hasenbanck/exa_tim/firmware/Src/power.c

#include "power.h"
#include "clock.h"
#include "config.h"
#include "main.h"
#include "stm32l0xx_hal.h"

extern LPTIM_HandleTypeDef hlptim1;
extern UART_HandleTypeDef hlpuart1;
extern RTC_HandleTypeDef hrtc;
extern SPI_HandleTypeDef hspi1;
extern TIM_HandleTypeDef htim2;

void HAL_TIM_MspPostInit(TIM_HandleTypeDef *htim);

void systemClockConfig(void) {
  RCC_OscInitTypeDef RCC_OscInitStruct;
  RCC_ClkInitTypeDef RCC_ClkInitStruct;
  RCC_PeriphCLKInitTypeDef PeriphClkInit;

  /* Configure the main internal regulator output voltage */
  __HAL_PWR_VOLTAGESCALING_CONFIG(PWR_REGULATOR_VOLTAGE_SCALE2);

  /*  Enable access to backup domain */
  HAL_PWR_EnableBkUpAccess();

  /* Configure LSE Drive Capability */
  __HAL_RCC_LSEDRIVE_CONFIG(RCC_LSEDRIVE_LOW);

  /* Initializes the CPU, AHB and APB busses clocks */
  RCC_OscInitStruct.OscillatorType =
      RCC_OSCILLATORTYPE_HSI | RCC_OSCILLATORTYPE_LSE;
  RCC_OscInitStruct.LSEState = RCC_LSE_ON;
  RCC_OscInitStruct.HSIState = RCC_HSI_ON;
  RCC_OscInitStruct.HSICalibrationValue = 16;
  RCC_OscInitStruct.PLL.PLLState = RCC_PLL_NONE;
  if (HAL_RCC_OscConfig(&RCC_OscInitStruct) != HAL_OK) {
    Error_Handler();
  }

  /* Initializes the CPU, AHB and APB busses clocks */
  RCC_ClkInitStruct.ClockType = RCC_CLOCKTYPE_HCLK | RCC_CLOCKTYPE_SYSCLK |
                                RCC_CLOCKTYPE_PCLK1 | RCC_CLOCKTYPE_PCLK2;
  RCC_ClkInitStruct.SYSCLKSource = RCC_SYSCLKSOURCE_HSI;
  RCC_ClkInitStruct.AHBCLKDivider = RCC_SYSCLK_DIV1;
  RCC_ClkInitStruct.APB1CLKDivider = RCC_HCLK_DIV1;
  RCC_ClkInitStruct.APB2CLKDivider = RCC_HCLK_DIV1;

  if (HAL_RCC_ClockConfig(&RCC_ClkInitStruct, FLASH_LATENCY_1) != HAL_OK) {
    Error_Handler();
  }

  PeriphClkInit.PeriphClockSelection =
      RCC_PERIPHCLK_LPUART1 | RCC_PERIPHCLK_RTC | RCC_PERIPHCLK_LPTIM1;
  PeriphClkInit.Lpuart1ClockSelection = RCC_LPUART1CLKSOURCE_LSE;
  PeriphClkInit.RTCClockSelection = RCC_RTCCLKSOURCE_LSE;
  PeriphClkInit.LptimClockSelection = RCC_LPTIM1CLKSOURCE_LSE;
  if (HAL_RCCEx_PeriphCLKConfig(&PeriphClkInit) != HAL_OK) {
    Error_Handler();
  }

#ifndef NDEBUG
  /* Activate debug clock */
  __HAL_RCC_DBGMCU_CLK_ENABLE();
#endif

  /* Configure the Systick interrupt time */
  HAL_SYSTICK_Config(HAL_RCC_GetHCLKFreq() / 1000);

  /* Configure the Systick */
  HAL_SYSTICK_CLKSourceConfig(SYSTICK_CLKSOURCE_HCLK);

  /* SysTick_IRQn interrupt configuration */
  HAL_NVIC_SetPriority(SysTick_IRQn, 0, 0);
}

void initGPIO(void) {
  GPIO_InitTypeDef GPIO_InitStruct;

  /* GPIO Ports Clock Enable */
  __HAL_RCC_GPIOC_CLK_ENABLE();
  __HAL_RCC_GPIOA_CLK_ENABLE();
  __HAL_RCC_GPIOB_CLK_ENABLE();

  /* Configure GPIO pin Output Level */
  HAL_GPIO_WritePin(GPIOA, CS_Pin | DISP_EN_Pin, GPIO_PIN_RESET);
  HAL_GPIO_WritePin(GPIOA, GNSS_EN_Pin, GPIO_PIN_SET); // Active LOW
  HAL_GPIO_WritePin(
      GPIOB, DC_Pin | RESET_Pin | BTN1_Pin | BTN2_Pin | BTN3_Pin | BTN4_Pin,
      GPIO_PIN_RESET);

  /* Configure GPIO pins : GNSS_EN_Pin CS_Pin DISP_EN_Pin */
  GPIO_InitStruct.Pin = GNSS_EN_Pin | CS_Pin | DISP_EN_Pin;
  GPIO_InitStruct.Mode = GPIO_MODE_OUTPUT_PP;
  GPIO_InitStruct.Pull = GPIO_NOPULL;
  GPIO_InitStruct.Speed = GPIO_SPEED_FREQ_LOW;
  HAL_GPIO_Init(GPIOA, &GPIO_InitStruct);

  /* Configure GPIO pin : BUSY_Pin */
  GPIO_InitStruct.Pin = BUSY_Pin;
  GPIO_InitStruct.Mode = GPIO_MODE_INPUT;
  GPIO_InitStruct.Pull = GPIO_NOPULL;
  HAL_GPIO_Init(GPIOA, &GPIO_InitStruct);

  /* Configure GPIO pins : DC_Pin RESET_Pin */
  GPIO_InitStruct.Pin = DC_Pin | RESET_Pin;
  GPIO_InitStruct.Mode = GPIO_MODE_OUTPUT_PP;
  GPIO_InitStruct.Pull = GPIO_NOPULL;
  GPIO_InitStruct.Speed = GPIO_SPEED_FREQ_LOW;
  HAL_GPIO_Init(GPIOB, &GPIO_InitStruct);

  /* Configure GPIO pins : BTN1_Pin BTN2_Pin BTN3_Pin BTN4_Pin */
  GPIO_InitStruct.Pin = BTN1_Pin | BTN2_Pin | BTN3_Pin | BTN4_Pin;
  GPIO_InitStruct.Mode = GPIO_MODE_INPUT;
  GPIO_InitStruct.Pull = GPIO_PULLDOWN;
  GPIO_InitStruct.Speed = GPIO_SPEED_FREQ_LOW;
  HAL_GPIO_Init(GPIOB, &GPIO_InitStruct);

  /* Configure GPIO pins : PA09 PA10 PA11 PA12 */
  GPIO_InitStruct.Pin = GPIO_PIN_9 | GPIO_PIN_10 | GPIO_PIN_11 | GPIO_PIN_12;
  GPIO_InitStruct.Mode = GPIO_MODE_ANALOG;
  GPIO_InitStruct.Pull = GPIO_NOPULL;
  HAL_GPIO_Init(GPIOA, &GPIO_InitStruct);
}

/* TIM2 init function */
void initTIM2(void) {
  TIM_OC_InitTypeDef sConfigOC;

  htim2.Instance = TIM2;
  htim2.Init.Prescaler = 1;
  htim2.Init.CounterMode = TIM_COUNTERMODE_UP;
  htim2.Init.Period = 1999;
  htim2.Init.ClockDivision = TIM_CLOCKDIVISION_DIV1;
  if (HAL_TIM_PWM_Init(&htim2) != HAL_OK) {
    Error_Handler();
  }

  sConfigOC.OCMode = TIM_OCMODE_PWM1;
  sConfigOC.Pulse = 999;
  sConfigOC.OCPolarity = TIM_OCPOLARITY_HIGH;
  sConfigOC.OCFastMode = TIM_OCFAST_DISABLE;
  if (HAL_TIM_PWM_ConfigChannel(&htim2, &sConfigOC, TIM_CHANNEL_2) != HAL_OK) {
    Error_Handler();
  }

  HAL_TIM_MspPostInit(&htim2);
}

void initRTC(void) {
  RTC_TimeTypeDef sTime;
  RTC_DateTypeDef sDate;

  /* Initialize RTC Only */
  hrtc.Instance = RTC;
  hrtc.Init.HourFormat = RTC_HOURFORMAT_24;
  hrtc.Init.AsynchPrediv = 127;
  hrtc.Init.SynchPrediv = 255;
  hrtc.Init.OutPut = RTC_OUTPUT_DISABLE;
  hrtc.Init.OutPutRemap = RTC_OUTPUT_REMAP_NONE;
  hrtc.Init.OutPutPolarity = RTC_OUTPUT_POLARITY_HIGH;
  hrtc.Init.OutPutType = RTC_OUTPUT_TYPE_OPENDRAIN;
  if (HAL_RTC_Init(&hrtc) != HAL_OK) {
    Error_Handler();
  }

  // We don't need to do further RTC configuration when coming back from standby
  if (!(__HAL_PWR_GET_FLAG(PWR_FLAG_SB) && __HAL_PWR_GET_FLAG(PWR_FLAG_WU))) {
    /* Initialize RTC and set the Time and Date */
    sTime.Hours = 0;
    sTime.Minutes = 0;
    sTime.Seconds = 0;
    sTime.DayLightSaving = RTC_DAYLIGHTSAVING_NONE;
    sTime.StoreOperation = RTC_STOREOPERATION_RESET;
    if (HAL_RTC_SetTime(&hrtc, &sTime, RTC_FORMAT_BIN) != HAL_OK) {
      Error_Handler();
    }

    sDate.WeekDay = RTC_WEEKDAY_MONDAY;
    sDate.Month = RTC_MONTH_JANUARY;
    sDate.Date = 01;
    sDate.Year = 18;

    if (HAL_RTC_SetDate(&hrtc, &sDate, RTC_FORMAT_BIN) != HAL_OK) {
      Error_Handler();
    }
  }

  // Wait for RTC to come ready
  // clang-format off
  while (HAL_RTC_GetState(&hrtc) == HAL_RTC_STATE_BUSY);
  // clang-format on
}

/* LPTIM1 init function */
void initLPTIM1(void) {
  hlptim1.Instance = LPTIM1;
  hlptim1.Init.Clock.Source = LPTIM_CLOCKSOURCE_APBCLOCK_LPOSC;
  hlptim1.Init.Clock.Prescaler = LPTIM_PRESCALER_DIV16;
  hlptim1.Init.Trigger.Source = LPTIM_TRIGSOURCE_SOFTWARE;
  hlptim1.Init.OutputPolarity = LPTIM_OUTPUTPOLARITY_HIGH;
  hlptim1.Init.UpdateMode = LPTIM_UPDATE_IMMEDIATE;
  hlptim1.Init.CounterSource = LPTIM_COUNTERSOURCE_INTERNAL;
  if (HAL_LPTIM_Init(&hlptim1) != HAL_OK) {
    Error_Handler();
  }

  /* 32.768 kHz / 16 =  0.48828125 ms * 30 = 15ms a tick */
  if (HAL_LPTIM_Counter_Start_IT(&hlptim1, 29) != HAL_OK) {
    Error_Handler();
  }
}

/* LPUART1 init function */
void initLPUART1(void) {
  hlpuart1.Instance = LPUART1;
  hlpuart1.Init.BaudRate = 9600;
  hlpuart1.Init.WordLength = UART_WORDLENGTH_7B;
  hlpuart1.Init.StopBits = UART_STOPBITS_1;
  hlpuart1.Init.Parity = UART_PARITY_NONE;
  hlpuart1.Init.Mode = UART_MODE_TX_RX;
  hlpuart1.Init.HwFlowCtl = UART_HWCONTROL_NONE;
  hlpuart1.Init.OneBitSampling = UART_ONE_BIT_SAMPLE_DISABLE;
  hlpuart1.AdvancedInit.AdvFeatureInit = UART_ADVFEATURE_DMADISABLEONERROR_INIT;
  hlpuart1.AdvancedInit.DMADisableonRxError =
      UART_ADVFEATURE_DMA_DISABLEONRXERROR;
  if (HAL_UART_Init(&hlpuart1) != HAL_OK) {
    Error_Handler();
  }
}

/* SPI1 init function */
void initSPI1(void) {
  /* SPI1 parameter configuration */
  hspi1.Instance = SPI1;
  hspi1.Init.Mode = SPI_MODE_MASTER;
  hspi1.Init.Direction = SPI_DIRECTION_2LINES;
  hspi1.Init.DataSize = SPI_DATASIZE_8BIT;
  hspi1.Init.CLKPolarity = SPI_POLARITY_LOW;
  hspi1.Init.CLKPhase = SPI_PHASE_1EDGE;
  hspi1.Init.NSS = SPI_NSS_SOFT;
  hspi1.Init.BaudRatePrescaler = SPI_BAUDRATEPRESCALER_2;
  hspi1.Init.FirstBit = SPI_FIRSTBIT_MSB;
  hspi1.Init.TIMode = SPI_TIMODE_DISABLE;
  hspi1.Init.CRCCalculation = SPI_CRCCALCULATION_DISABLE;
  hspi1.Init.CRCPolynomial = 7;
  if (HAL_SPI_Init(&hspi1) != HAL_OK) {
    Error_Handler();
  }
}

void initPVD(void) {
  PWR_PVDTypeDef sConfigPVD;
  sConfigPVD.Mode = PWR_PVD_MODE_NORMAL;
  sConfigPVD.PVDLevel = PWR_PVDLEVEL_4; /* 0 = 1.9V
                                         * 1 = 2.1V
                                         * 2 = 2.3V
                                         * 3 = 2.5V
                                         * 4 = 2.7V
                                         * 5 = 2.9V
                                         * 6 = 3.1V
                                         */
  HAL_PWR_ConfigPVD(&sConfigPVD);
  HAL_PWR_EnablePVD();
}

void initNormalMode(void) {
  systemClockConfig();
  initGPIO();
  initTIM2();
  initLPTIM1();
  initRTC();
  initPVD();
  checkConfig();
}

void switchSleepMode(void) {
#ifndef NDEBUG
  HAL_DBGMCU_EnableDBGSleepMode();
#endif
  HAL_PWR_DisableBkUpAccess();
  HAL_PWR_EnterSLEEPMode(PWR_MAINREGULATOR_ON, PWR_STOPENTRY_WFI);
  HAL_PWR_EnableBkUpAccess();
}

void switchStopMode(void) {
#ifndef NDEBUG
  HAL_DBGMCU_EnableDBGStopMode();
#endif
  HAL_PWR_DisableBkUpAccess();
  HAL_PWR_DisablePVD();
  __HAL_PWR_CLEAR_FLAG(PWR_FLAG_WU);
  HAL_PWR_EnterSTOPMode(PWR_LOWPOWERREGULATOR_ON, PWR_STOPENTRY_WFI);
  systemClockConfig();
  HAL_PWR_EnableBkUpAccess();
}

void switchStandbyMode(void) {
#ifndef NDEBUG
  HAL_DBGMCU_EnableDBGStandbyMode();
#endif
  HAL_PWR_DisableBkUpAccess();
  HAL_PWR_DisablePVD();
  HAL_PWR_EnableWakeUpPin(PWR_WAKEUP_PIN1);
  __HAL_PWR_CLEAR_FLAG(PWR_FLAG_WU);
  HAL_PWR_EnterSTANDBYMode();
}
