hasenbanck/exa_tim/firmware/Inc/display.h

#pragma once

#include "u8g2.h"
#include "logic.h"
#include <stdbool.h>

void initDisplay(applicationState_t *state);
void drawDisplay(applicationState_t* state);
void powerOffDisplay(void);
void drawMenu(void);
bool isDisplayBusy(void);
